Morita-Ntyb/KM-01/KM-01_test/200906_KM-01_I2Ctest.ino

#include <Wire.h>
#include <SPI.h>
#include <SparkFunLSM9DS1.h>
#include <PCA9685.h>            //PCA9685用ヘッダーファイル（秋月電子通商作成）

PCA9685 pwm = PCA9685(0x40);    //PCA9685のアドレス指定（アドレスジャンパ未接続時）
PCA9685 pwm2 = PCA9685(0x41);   //PCA9685のアドレス指定（A0接続時）

#define SERVOMIN 150            //最小パルス幅 (標準的なサーボパルスに設定)
#define SERVOMAX 600            //最大パルス幅 (標準的なサーボパルスに設定)


//////////////////////////
// LSM9DS1 Library Init //
//////////////////////////
// Use the LSM9DS1 class to create an object. [imu] can be
// named anything, we'll refer to that throught the sketch.
LSM9DS1 imu;

///////////////////////
// Example I2C Setup //
///////////////////////
// SDO_XM and SDO_G are both pulled high, so our addresses are:
// #define LSM9DS1_M  0x1E // Would be 0x1C if SDO_M is LOW
// #define LSM9DS1_AG 0x6B // Would be 0x6A if SDO_AG is LOW

////////////////////////////
// Sketch Output Settings //
////////////////////////////
#define PRINT_CALCULATED
//#define PRINT_RAW
#define PRINT_SPEED 250 // 250 ms between prints
static unsigned long lastPrint = 0; // Keep track of print time

// Earth's magnetic field varies by location. Add or subtract
// a declination to get a more accurate heading. Calculate
// your's here:
// http://www.ngdc.noaa.gov/geomag-web/#declination
#define DECLINATION -8.58 // Declination (degrees) in Boulder, CO.

//Function definitions
void printGyro();
void printAccel();
void printMag();
void printAttitude(float ax, float ay, float az, float mx, float my, float mz);







void setup()
{
  pwm.begin();                   //初期設定 (アドレス0x40用)
  pwm.setPWMFreq(60);            //PWM周期を60Hzに設定 (アドレス0x40用)

  
  Serial.begin(115200);

  Wire.begin();

  if (imu.begin() == false) // with no arguments, this uses default addresses (AG:0x6B, M:0x1E) and i2c port (Wire).
  {
    Serial.println("Failed to communicate with LSM9DS1.");
    Serial.println("Double-check wiring.");
    Serial.println("Default settings in this sketch will " \
                   "work for an out of the box LSM9DS1 " \
                   "Breakout, but may need to be modified " \
                   "if the board jumpers are.");
    while (1);
  }
}



int n=0;

int a=0;

void loop()
{
  // Update the sensor values whenever new data is available
  if ( imu.gyroAvailable() )
  {
    // To read from the gyroscope,  first call the
    // readGyro() function. When it exits, it'll update the
    // gx, gy, and gz variables with the most current data.
    imu.readGyro();
  }
  if ( imu.accelAvailable() )
  {
    // To read from the accelerometer, first call the
    // readAccel() function. When it exits, it'll update the
    // ax, ay, and az variables with the most current data.
    imu.readAccel();
  }
  if ( imu.magAvailable() )
  {
    // To read from the magnetometer, first call the
    // readMag() function. When it exits, it'll update the
    // mx, my, and mz variables with the most current data.
    imu.readMag();
  }

  if ((lastPrint + PRINT_SPEED) < millis())
  {
    printGyro();  // Print "G: gx, gy, gz"
    printAccel(); // Print "A: ax, ay, az"
    printMag();   // Print "M: mx, my, mz"
    // Print the heading and orientation for fun!
    // Call print attitude. The LSM9DS1's mag x and y
    // axes are opposite to the accelerometer, so my, mx are
    // substituted for each other.
    printAttitude(imu.ax, imu.ay, imu.az,
                  -imu.my, -imu.mx, imu.mz);
    Serial.println();

    lastPrint = millis(); // Update lastPrint time
  }




    for(int i=0; i<2; i++)
      servo_write(i,n);



  if(n>=170)
  {
    a=1;
  }
  if(n<=10)
  {
    a=0;
  }



if(a==1)
{
    n=n-1;
}
if(a==0)
{
    n=n+1;
}


  
}

void printGyro()
{
  // Now we can use the gx, gy, and gz variables as we please.
  // Either print them as raw ADC values, or calculated in DPS.
  Serial.print("G: ");
#ifdef PRINT_CALCULATED
  // If you want to print calculated values, you can use the
  // calcGyro helper function to convert a raw ADC value to
  // DPS. Give the function the value that you want to convert.
  Serial.print(imu.calcGyro(imu.gx), 2);
  Serial.print(", ");
  Serial.print(imu.calcGyro(imu.gy), 2);
  Serial.print(", ");
  Serial.print(imu.calcGyro(imu.gz), 2);
  Serial.println(" deg/s");
#elif defined PRINT_RAW
  Serial.print(imu.gx);
  Serial.print(", ");
  Serial.print(imu.gy);
  Serial.print(", ");
  Serial.println(imu.gz);
#endif
}

void printAccel()
{
  // Now we can use the ax, ay, and az variables as we please.
  // Either print them as raw ADC values, or calculated in g's.
  Serial.print("A: ");
#ifdef PRINT_CALCULATED
  // If you want to print calculated values, you can use the
  // calcAccel helper function to convert a raw ADC value to
  // g's. Give the function the value that you want to convert.
  Serial.print(imu.calcAccel(imu.ax), 2);
  Serial.print(", ");
  Serial.print(imu.calcAccel(imu.ay), 2);
  Serial.print(", ");
  Serial.print(imu.calcAccel(imu.az), 2);
  Serial.println(" g");
#elif defined PRINT_RAW
  Serial.print(imu.ax);
  Serial.print(", ");
  Serial.print(imu.ay);
  Serial.print(", ");
  Serial.println(imu.az);
#endif

}

void printMag()
{
  // Now we can use the mx, my, and mz variables as we please.
  // Either print them as raw ADC values, or calculated in Gauss.
  Serial.print("M: ");
#ifdef PRINT_CALCULATED
  // If you want to print calculated values, you can use the
  // calcMag helper function to convert a raw ADC value to
  // Gauss. Give the function the value that you want to convert.
  Serial.print(imu.calcMag(imu.mx), 2);
  Serial.print(", ");
  Serial.print(imu.calcMag(imu.my), 2);
  Serial.print(", ");
  Serial.print(imu.calcMag(imu.mz), 2);
  Serial.println(" gauss");
#elif defined PRINT_RAW
  Serial.print(imu.mx);
  Serial.print(", ");
  Serial.print(imu.my);
  Serial.print(", ");
  Serial.println(imu.mz);
#endif
}

// Calculate pitch, roll, and heading.
// Pitch/roll calculations take from this app note:
// http://cache.freescale.com/files/sensors/doc/app_note/AN3461.pdf?fpsp=1
// Heading calculations taken from this app note:
// http://www51.honeywell.com/aero/common/documents/myaerospacecatalog-documents/Defense_Brochures-documents/Magnetic__Literature_Application_notes-documents/AN203_Comp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
void printAttitude(float ax, float ay, float az, float mx, float my, float mz)
{
  float roll = atan2(ay, az);
  float pitch = atan2(-ax, sqrt(ay * ay + az * az));

  float heading;
  if (my == 0)
    heading = (mx < 0) ? PI : 0;
  else
    heading = atan2(mx, my);

  heading -= DECLINATION * PI / 180;

  if (heading > PI) heading -= (2 * PI);
  else if (heading < -PI) heading += (2 * PI);

  // Convert everything from radians to degrees:
  heading *= 180.0 / PI;
  pitch *= 180.0 / PI;
  roll  *= 180.0 / PI;

  Serial.print("Pitch, Roll: ");
  Serial.print(pitch, 2);
  Serial.print(", ");
  Serial.println(roll, 2);
  Serial.print("Heading: "); Serial.println(heading, 2);
}




void servo_write(int ch, int ang){ //動かすサーボチャンネルと角度を指定
  ang = map(ang, 0, 180, SERVOMIN, SERVOMAX); //角度（0～180）をPWMのパルス幅（150～600）に変換
  pwm.setPWM(ch, 0, ang);
  pwm2.setPWM(ch, 0, ang);
  //delay(1);
}
